Forairaaaaa/Chappie-II/Pics/IMG_5138.JPG

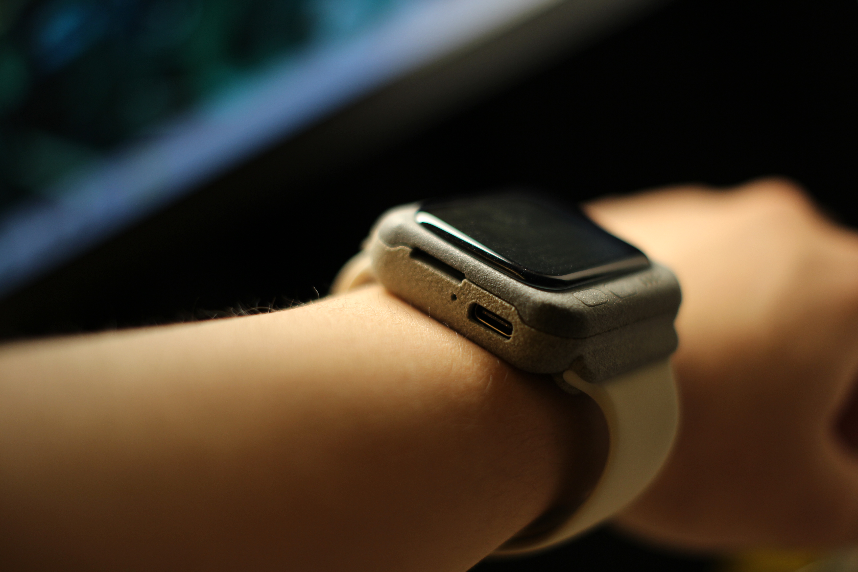
Pics/IMG_5138.JPG
