Forairaaaaa/Chappie-II/Pics/IMG_5139.JPG

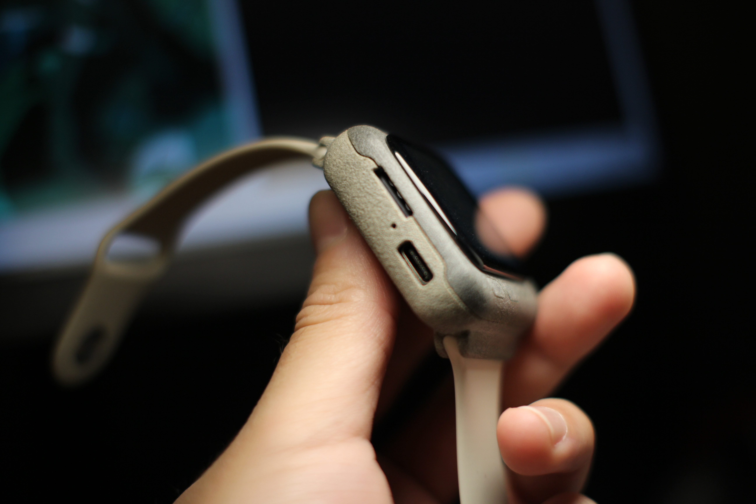
Pics/IMG_5139.JPG
