Forairaaaaa/Chappie-II/Firmware/src/ChappieBsp/EmmaBSP/Display/EmmaDisplay.hpp

/**
 * @file EmmaDisplay.hpp
 * @author Forairaaaaa
 * @brief 
 * @version 0.1
 * @date 2023-02-27
 * 
 * @copyright Copyright (c) 2023
 * 
 */
#pragma once
#include "../../EmmaConfig.h"
#if EMMA_MODULE_DISPLAY

#include <LovyanGFX.hpp>

/* If not, setup your own config here */
/* https://github.com/lovyan03/LovyanGFX/blob/master/src/lgfx_user/LGFX_ESP32_sample.hpp */
#ifndef LGFX_AUTODETECT

/// 独自の設定を行うクラスを、LGFX_Deviceから派生して作成します。
class LGFX_EmmaDisplay : public lgfx::LGFX_Device
{
/*
 クラス名は"LGFX"から別の名前に変更しても構いません。
 AUTODETECTと併用する場合は"LGFX"は使用されているため、LGFX以外の名前に変更してください。
 また、複数枚のパネルを同時使用する場合もそれぞれに異なる名前を付けてください。
 ※ クラス名を変更する場合はコンストラクタの名前も併せて同じ名前に変更が必要です。

 名前の付け方は自由に決めて構いませんが、設定が増えた場合を想定し、
 例えばESP32 DevKit-CでSPI接続のILI9341の設定を行った場合、
  LGFX_DevKitC_SPI_ILI9341
 のような名前にし、ファイル名とクラス名を一致させておくことで、利用時に迷いにくくなります。
//*/


// 接続するパネルの型にあったインスタンスを用意します。
//lgfx::Panel_GC9A01      _panel_instance;
//lgfx::Panel_GDEW0154M09 _panel_instance;
//lgfx::Panel_HX8357B     _panel_instance;
//lgfx::Panel_HX8357D     _panel_instance;
//lgfx::Panel_ILI9163     _panel_instance;
//   lgfx::Panel_ILI9341     _panel_instance;
//lgfx::Panel_ILI9342     _panel_instance;
//lgfx::Panel_ILI9481     _panel_instance;
//lgfx::Panel_ILI9486     _panel_instance;
//lgfx::Panel_ILI9488     _panel_instance;
//lgfx::Panel_IT8951      _panel_instance;
//lgfx::Panel_RA8875      _panel_instance;
//lgfx::Panel_SH110x      _panel_instance; // SH1106, SH1107
//lgfx::Panel_SSD1306     _panel_instance;
//lgfx::Panel_SSD1327     _panel_instance;
//lgfx::Panel_SSD1331     _panel_instance;
//lgfx::Panel_SSD1351     _panel_instance; // SSD1351, SSD1357
//lgfx::Panel_SSD1963     _panel_instance;
//lgfx::Panel_ST7735      _panel_instance;
//lgfx::Panel_ST7735S     _panel_instance;
lgfx::Panel_ST7789      _panel_instance;
//lgfx::Panel_ST7796      _panel_instance;


// パネルを接続するバスの種類にあったインスタンスを用意します。
  lgfx::Bus_SPI       _bus_instance;   // SPIバスのインスタンス
//lgfx::Bus_I2C       _bus_instance;   // I2Cバスのインスタンス (ESP32のみ)
//lgfx::Bus_Parallel8 _bus_instance;   // 8ビットパラレルバスのインスタンス (ESP32のみ)

// バックライト制御が可能な場合はインスタンスを用意します。(必要なければ削除)
  lgfx::Light_PWM     _light_instance;

public:

  // コンストラクタを作成し、ここで各種設定を行います。
  // クラス名を変更した場合はコンストラクタも同じ名前を指定してください。
  LGFX_EmmaDisplay(void)
  {
    { // バス制御の設定を行います。
      auto cfg = _bus_instance.config();    // バス設定用の構造体を取得します。

// SPIバスの設定
      cfg.spi_host = SPI3_HOST;     // 使用するSPIを選択  ESP32-S2,C3 : SPI2_HOST or SPI3_HOST / ESP32 : VSPI_HOST or HSPI_HOST
      // ※ ESP-IDFバージョンアップに伴い、VSPI_HOST , HSPI_HOSTの記述は非推奨になるため、エラーが出る場合は代わりにSPI2_HOST , SPI3_HOSTを使用してください。
      cfg.spi_mode = 2;             // SPI通信モードを設定 (0 ~ 3)
      cfg.freq_write = 80000000;    // 送信時のSPIクロック (最大80MHz, 80MHzを整数で割った値に丸められます)
      cfg.freq_read  = 16000000;    // 受信時のSPIクロック
      cfg.spi_3wire  = true;        // 受信をMOSIピンで行う場合はtrueを設定
      cfg.use_lock   = true;        // トランザクションロックを使用する場合はtrueを設定
      cfg.dma_channel = SPI_DMA_CH_AUTO; // 使用するDMAチャンネルを設定 (0=DMA不使用 / 1=1ch / 2=ch / SPI_DMA_CH_AUTO=自動設定)
      // ※ ESP-IDFバージョンアップに伴い、DMAチャンネルはSPI_DMA_CH_AUTO(自動設定)が推奨になりました。1ch,2chの指定は非推奨になります。
      cfg.pin_sclk = 40;            // SPIのSCLKピン番号を設定
      cfg.pin_mosi = 41;            // SPIのMOSIピン番号を設定
      cfg.pin_miso = -1;            // SPIのMISOピン番号を設定 (-1 = disable)
      cfg.pin_dc   = 38;            // SPIのD/Cピン番号を設定  (-1 = disable)
     // SDカードと共通のSPIバスを使う場合、MISOは省略せず必ず設定してください。
//*/


      _bus_instance.config(cfg);    // 設定値をバスに反映します。
      _panel_instance.setBus(&_bus_instance);      // バスをパネルにセットします。
    }

    { // 表示パネル制御の設定を行います。
      auto cfg = _panel_instance.config();    // 表示パネル設定用の構造体を取得します。

      cfg.pin_cs           =    39;  // CSが接続されているピン番号   (-1 = disable)
      cfg.pin_rst          =    47;  // RSTが接続されているピン番号  (-1 = disable)
      cfg.pin_busy         =    -1;  // BUSYが接続されているピン番号 (-1 = disable)

      // ※ 以下の設定値はパネル毎に一般的な初期値が設定されていますので、不明な項目はコメントアウトして試してみてください。

      cfg.panel_width      =   240;  // 実際に表示可能な幅
      cfg.panel_height     =   280;  // 実際に表示可能な高さ
      cfg.offset_x         =     0;  // パネルのX方向オフセット量
      cfg.offset_y         =     20;  // パネルのY方向オフセット量
      cfg.offset_rotation  =     1;  // 回転方向の値のオフセット 0~7 (4~7は上下反転)
      cfg.dummy_read_pixel =     8;  // ピクセル読出し前のダミーリードのビット数
      cfg.dummy_read_bits  =     1;  // ピクセル以外のデータ読出し前のダミーリードのビット数
      cfg.readable         =  true;  // データ読出しが可能な場合 trueに設定
      cfg.invert           = true;  // パネルの明暗が反転してしまう場合 trueに設定
      cfg.rgb_order        = true;  // パネルの赤と青が入れ替わってしまう場合 trueに設定
      cfg.dlen_16bit       = false;  // 16bitパラレルやSPIでデータ長を16bit単位で送信するパネルの場合 trueに設定
      cfg.bus_shared       =  true;  // SDカードとバスを共有している場合 trueに設定(drawJpgFile等でバス制御を行います)

// 以下はST7735やILI9163のようにピクセル数が可変のドライバで表示がずれる場合にのみ設定してください。
//    cfg.memory_width     =   240;  // ドライバICがサポートしている最大の幅
//    cfg.memory_height    =   320;  // ドライバICがサポートしている最大の高さ

      _panel_instance.config(cfg);
    }

//*
    { // バックライト制御の設定を行います。（必要なければ削除）
      auto cfg = _light_instance.config();    // バックライト設定用の構造体を取得します。

      cfg.pin_bl = 45;              // バックライトが接続されているピン番号
      cfg.invert = false;           // バックライトの輝度を反転させる場合 true
      cfg.freq   = 44100;           // バックライトのPWM周波数
      cfg.pwm_channel = 7;          // 使用するPWMのチャンネル番号

      _light_instance.config(cfg);
      _panel_instance.setLight(&_light_instance);  // バックライトをパネルにセットします。
    }
//*/

    setPanel(&_panel_instance); // 使用するパネルをセットします。
  }
};
#endif

#endif
